jonathan-iap/CoilWinder/img/2016-08-17 12.49.52.jpg

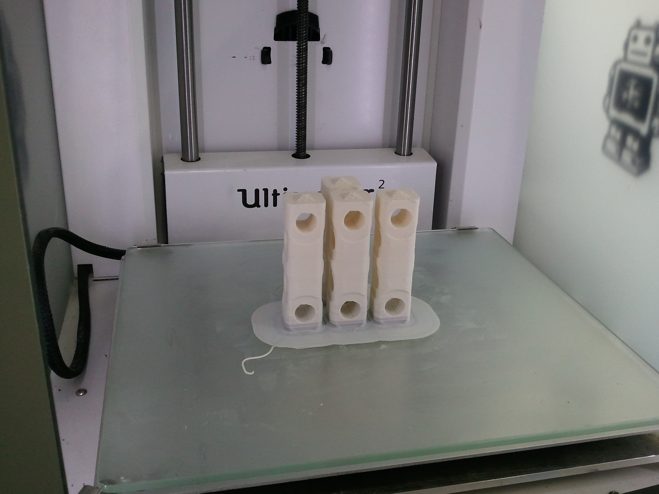
img/2016-08-17 12.49.52.jpg
