jonathan-iap/CoilWinder/img/2016-08-17 14.06.52.jpg

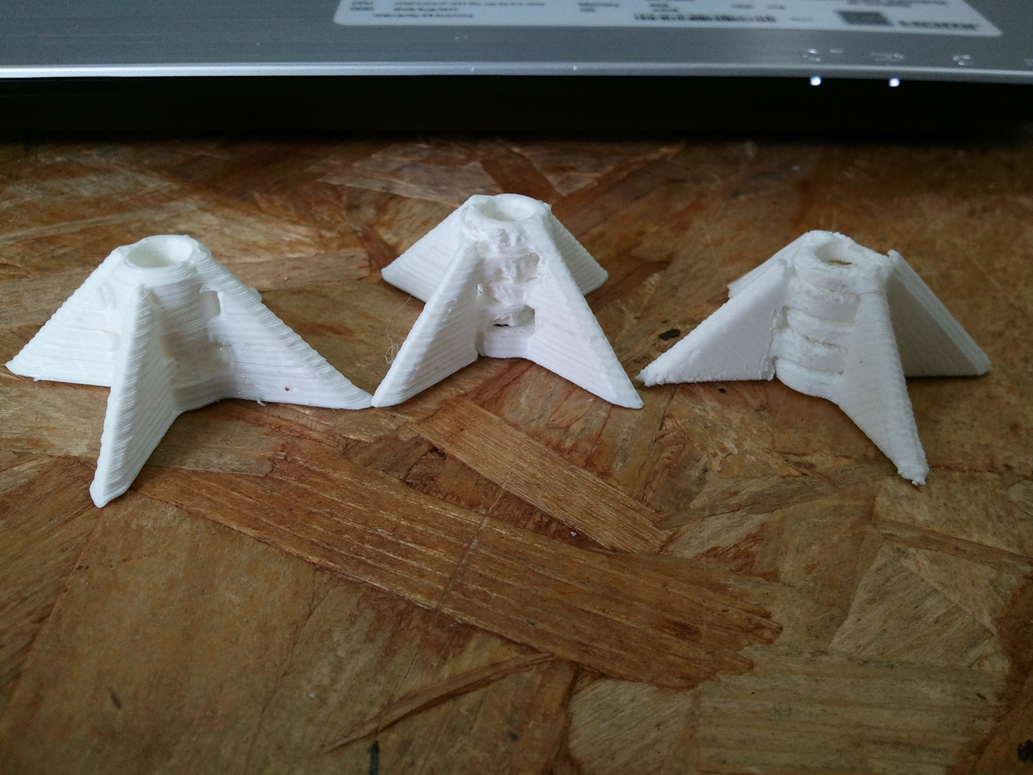
img/2016-08-17 14.06.52.jpg
