jonathan-iap/CoilWinder/img/2016-08-17 15.03.24.jpg

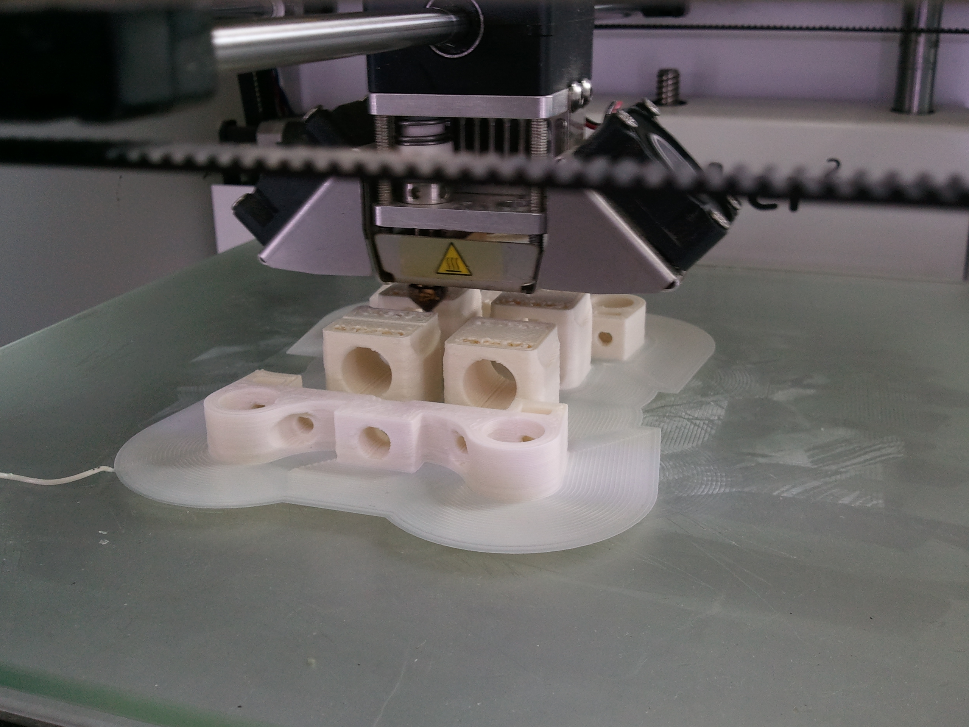
img/2016-08-17 15.03.24.jpg
