jonathan-iap/CoilWinder/img/2016-08-17 15.03.32.jpg

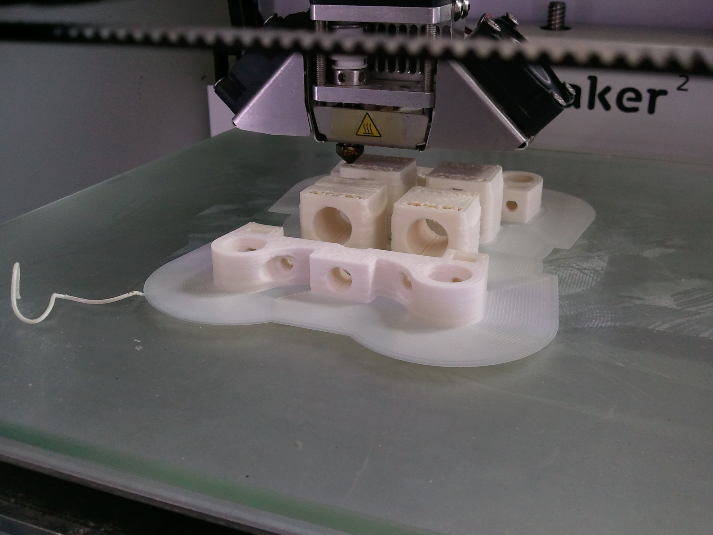
img/2016-08-17 15.03.32.jpg
