jonathan-iap/CoilWinder/img/2016-08-17 15.18.49.jpg

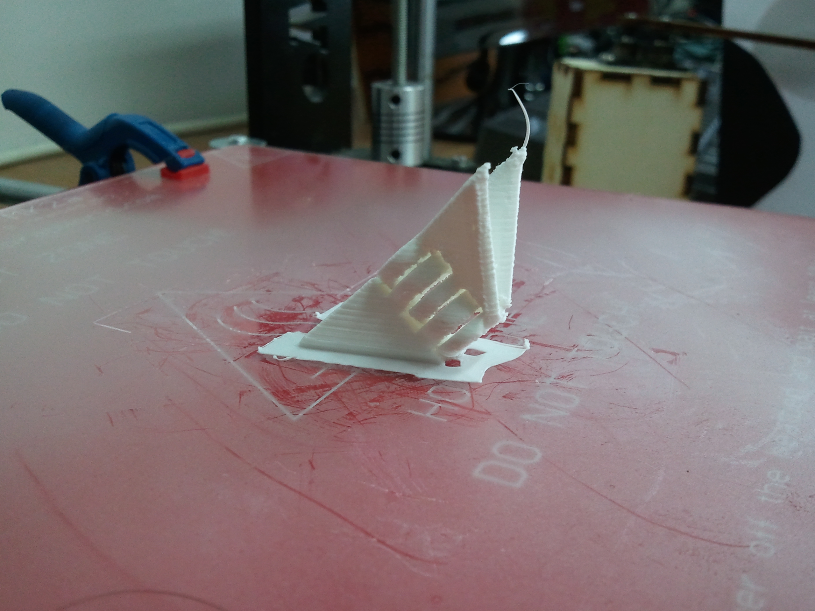
img/2016-08-17 15.18.49.jpg
