jonathan-iap/CoilWinder/img/2016-08-17 17.17.26.jpg

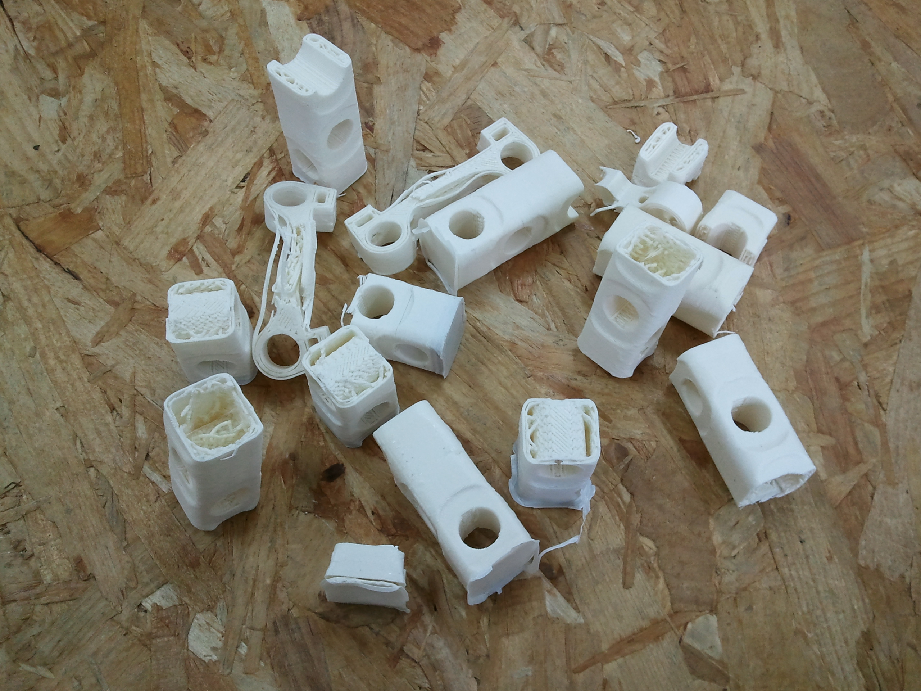
img/2016-08-17 17.17.26.jpg
