jonathan-iap/CoilWinder/img/2016-08-18 11.39.42.jpg

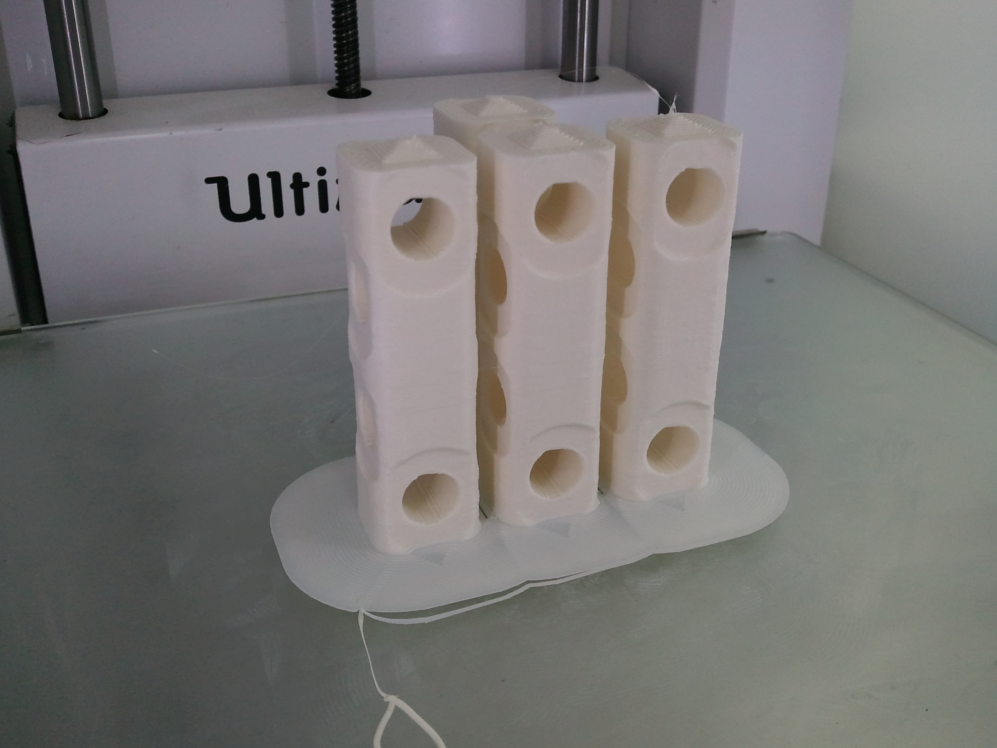
img/2016-08-18 11.39.42.jpg
