jonathan-iap/CoilWinder/img/2016-08-18 16.04.44.jpg

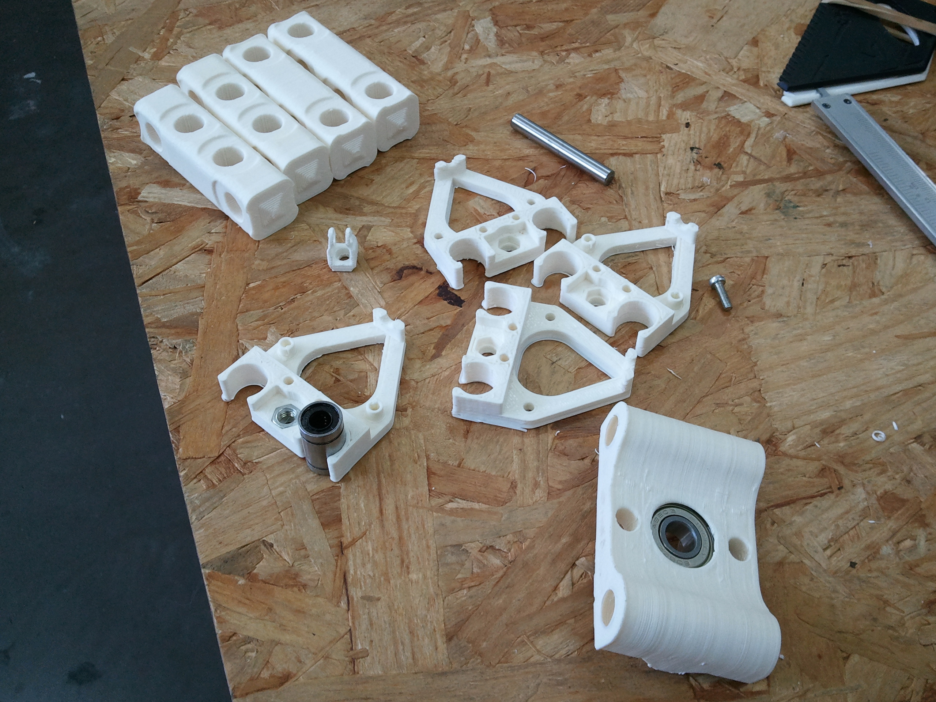
img/2016-08-18 16.04.44.jpg
