jonathan-iap/CoilWinder/img/2016-08-19 11.20.56.jpg

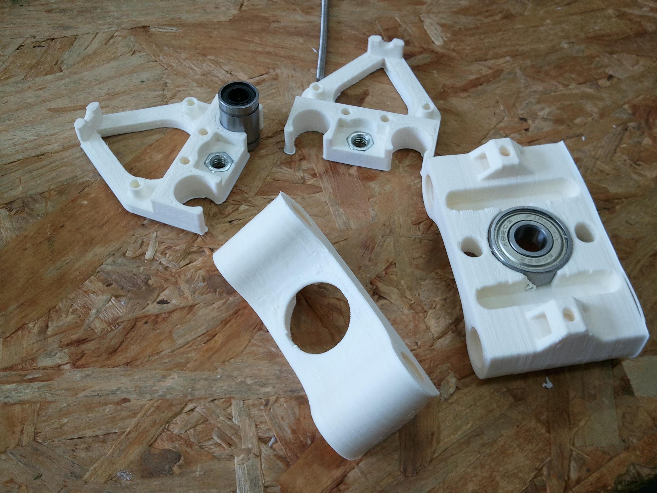
img/2016-08-19 11.20.56.jpg
