jonathan-iap/CoilWinder/img/2016-09-03 12.59.46.jpg

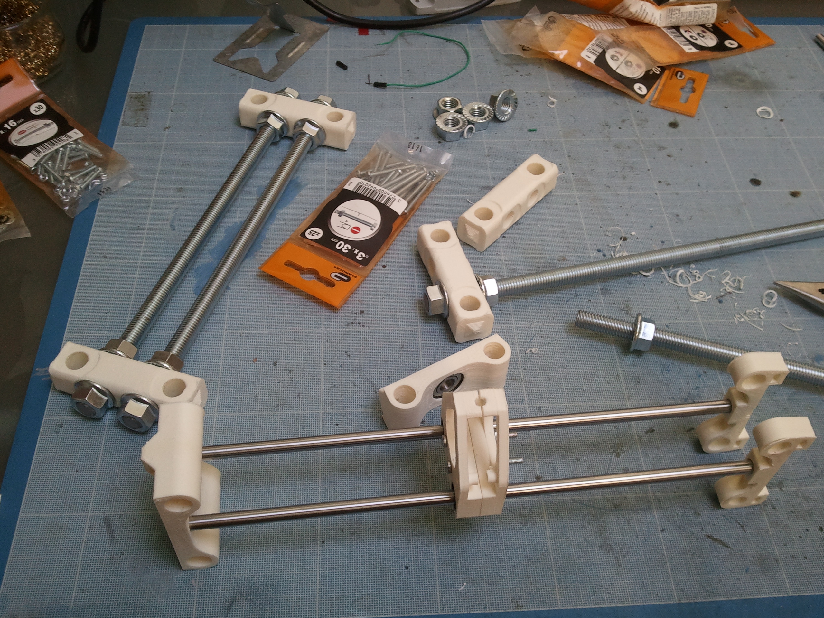
img/2016-09-03 12.59.46.jpg
