jonathan-iap/CoilWinder/img/2016-09-10 18.06.44.jpg

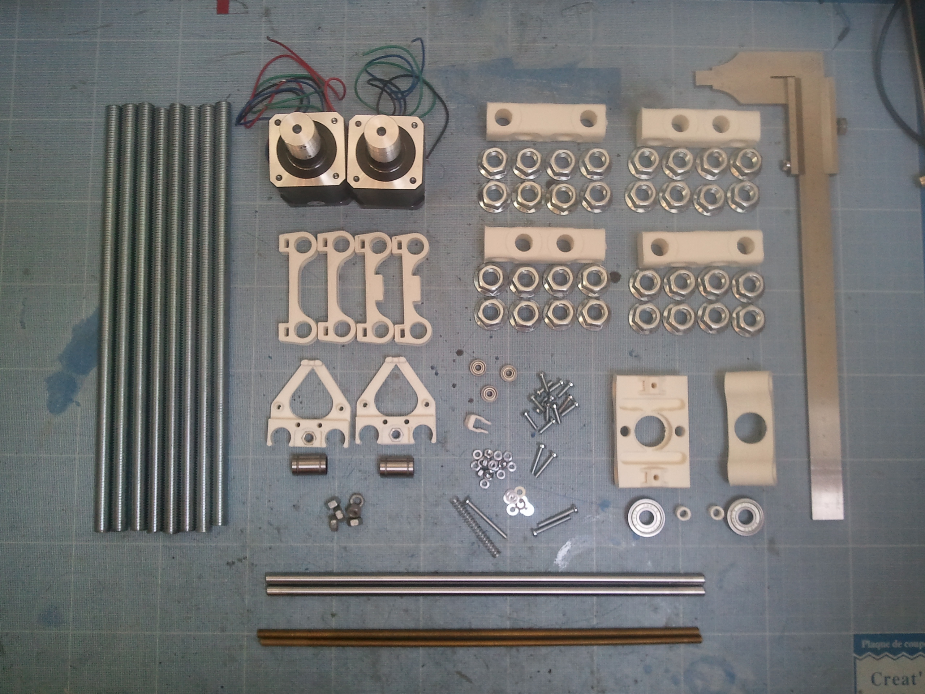
img/2016-09-10 18.06.44.jpg
