jonathan-iap/CoilWinder/img/2016-09-10 18.12.28.jpg

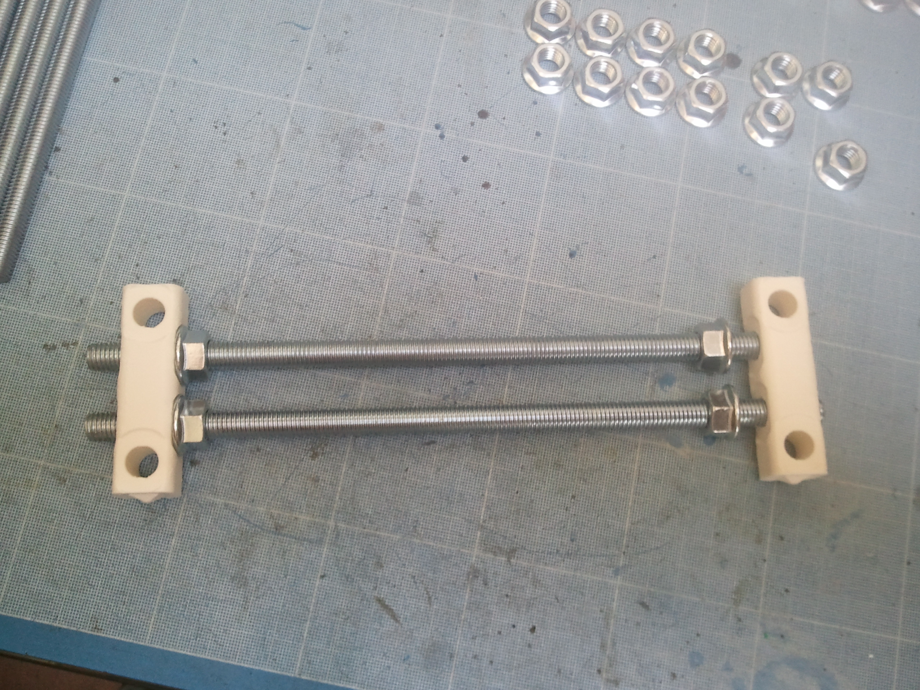
img/2016-09-10 18.12.28.jpg
