jonathan-iap/CoilWinder/img/2016-09-10 18.24.47.jpg

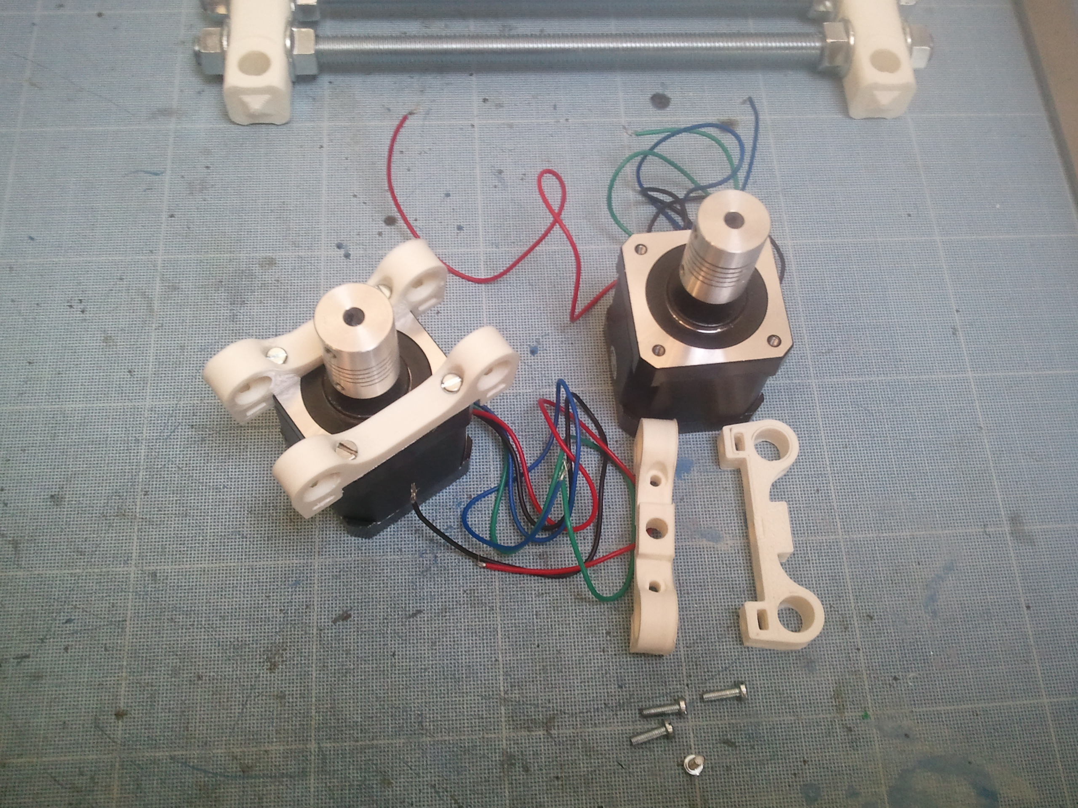
img/2016-09-10 18.24.47.jpg
