jonathan-iap/CoilWinder/img/2016-09-10 19.26.21.jpg

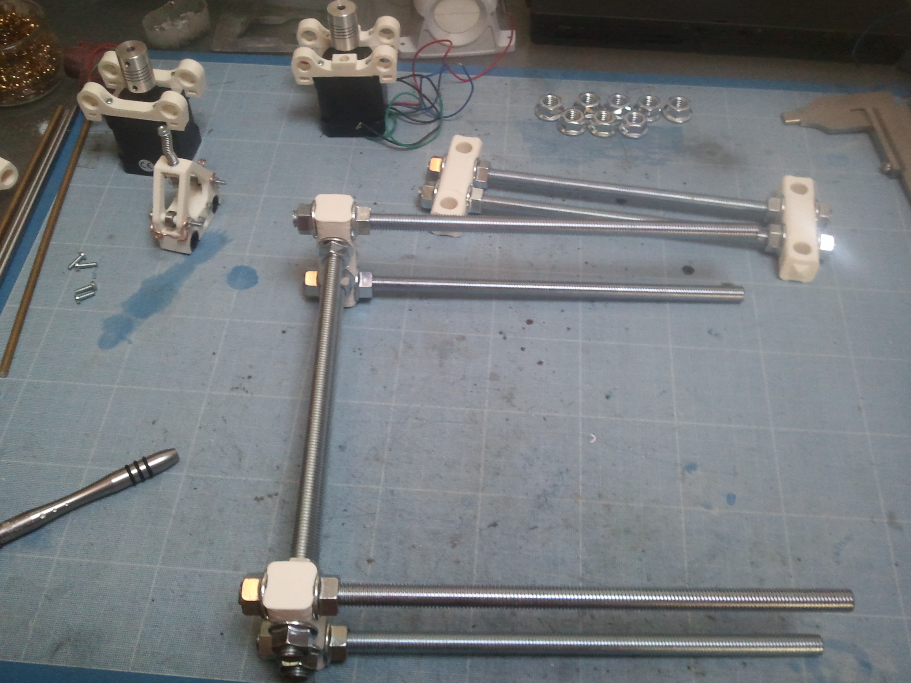
img/2016-09-10 19.26.21.jpg
