jonathan-iap/CoilWinder/img/2016-09-10 19.38.29.jpg

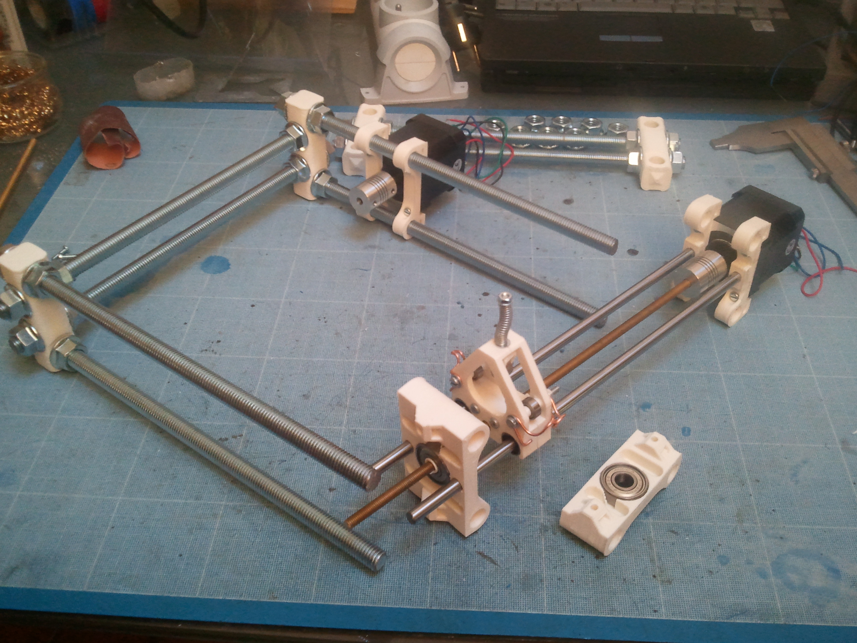
img/2016-09-10 19.38.29.jpg
