jonathan-iap/CoilWinder/img/2016-09-10 20.13.05.jpg

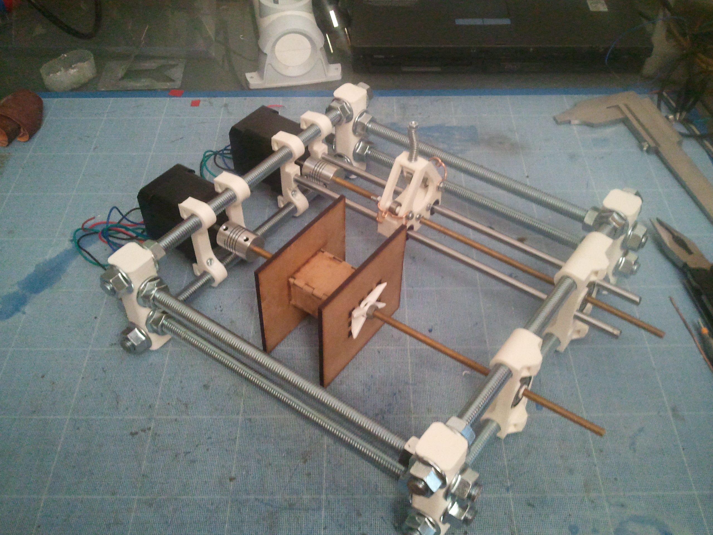
img/2016-09-10 20.13.05.jpg
