jonathan-iap/CoilWinder/img/2016-10-08 19.07.40.jpg

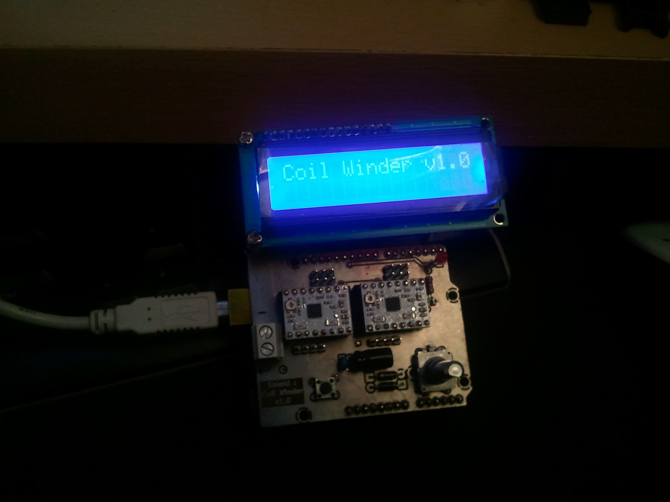
img/2016-10-08 19.07.40.jpg
