jonathan-iap/CoilWinder/img/2016-10-08 19.10.43.jpg

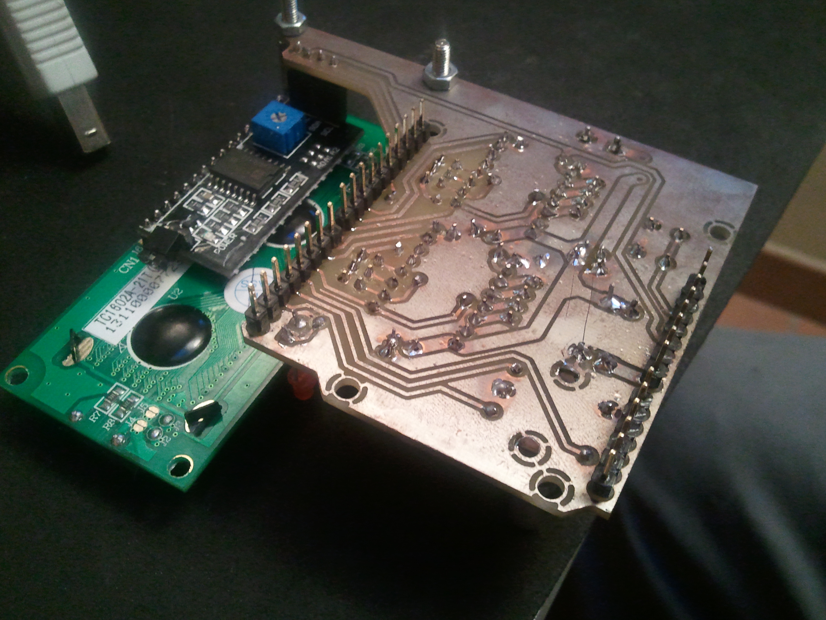
img/2016-10-08 19.10.43.jpg
