jonathan-iap/CoilWinder/img/2016-10-08 19.12.30.jpg

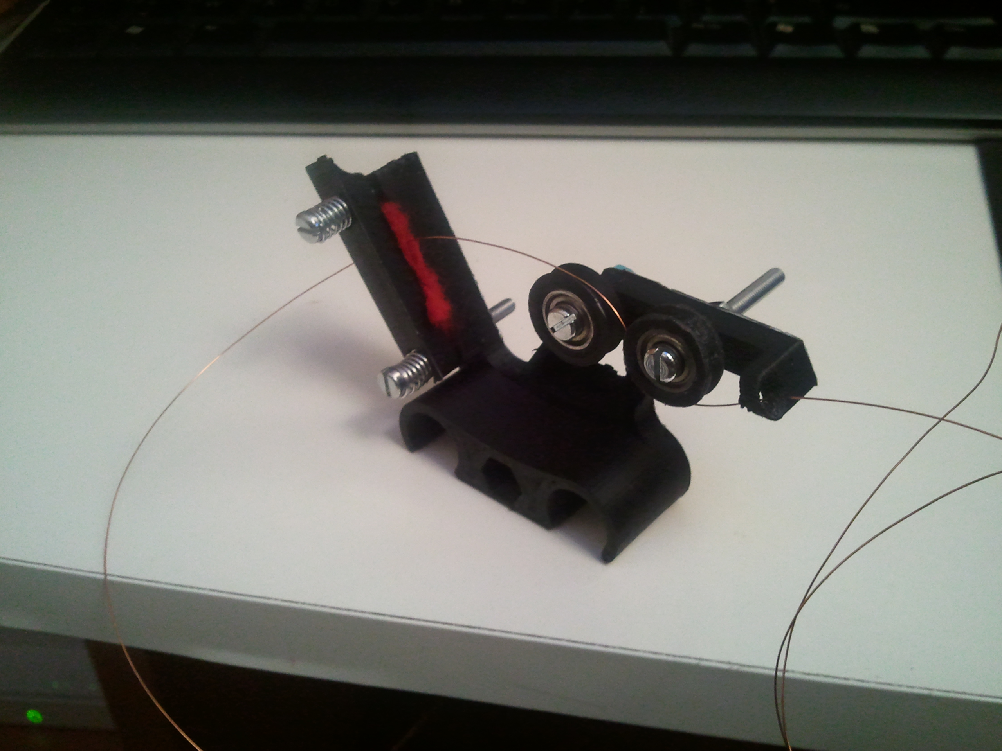
img/2016-10-08 19.12.30.jpg
