jonathan-iap/CoilWinder/STL_export/coin.stl

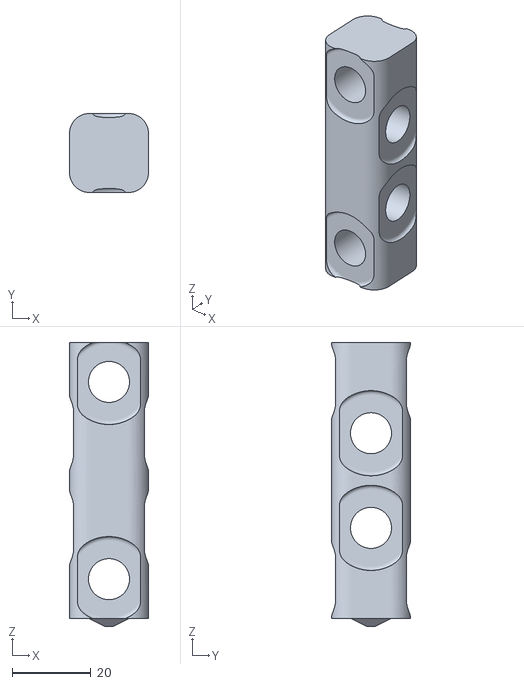
[picture p47: CAD file, 2017-12-31]
STL_export/coin.stl
20.0 x 20.0 x 72.0
