jonathan-iap/CoilWinder/STL_export/support axe guide fil_v0.2.stl

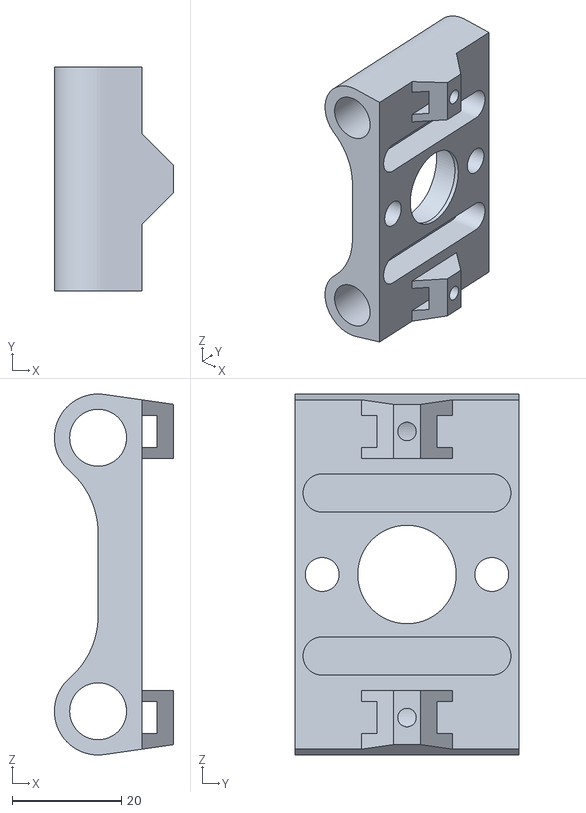
[picture p48: CAD file, 2017-12-29]
STL_export/support axe guide fil_v0.2.stl
21.8 x 41.0 x 66.0
