jonathan-iap/CoilWinder/Arduino/src/Motor.h

#ifndef MOTOR_H
#define MOTOR_H

#include "Arduino.h"
#include "Configuration.h"
#include "Fastio.h"
#include "TimerOne.h"

#define COIL      1
#define CARRIAGE  2

#define ACC 1000

#define MOTOR_INT 10 // motor interrupt in microseconds
#define RPM_TO_INT(rpm) ((600000 / rpm) / STEPS_PER_TR * MOTOR_INT)

#define WINDING   1
#define TRAVELING 2
#define ROTATION  3

void M_init();
void M_start();
void M_stop();
void M_engine();

void oneStep(bool M_coil, bool M_carr);
void updateCounter();

uint16_t M_getCoilTr();
bool M_getWindingStatus();
float M_getDisplacement();

void M_setMotors(bool M_coil, bool M_coilDir, bool M_carr, bool M_carrDir, uint16_t speed);
uint16_t M_setSpeed(uint16_t speed);
void M_invertSense();
void M_setSimpleDisplacement(uint8_t action, uint16_t pass, uint16_t steps);
void M_setWindingDisplacement(uint16_t pass, uint16_t steps, uint16_t tr,
			      uint16_t stepsTr, bool fastest);
void M_setWindingCounter(bool isNewCoil, bool isSuperior, uint16_t interval, uint16_t rest, uint16_t add);
void M_setState(bool isResume, uint16_t carrPass, uint16_t carrSteps, uint16_t coilTr, uint16_t coilSteps);
void M_getState(uint16_t *p_carrPass, uint16_t *p_carrSteps, bool *p_carrDir,
		uint16_t *p_coilTr, uint16_t *p_coilSteps, bool *p_coilDir);


#endif
