jonathan-iap/CoilWinder/Arduino/src/Fastio.h

/**
 * From Marlin 3D Printer Firmware
 * Copyright (C) 2016 MarlinFirmware [https://github.com/MarlinFirmware/Marlin]
 *
 * Based on Sprinter and grbl.
 * Copyright (C) 2011 Camiel Gubbels / Erik van der Zalm
 *
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
 */

/**
  This code contributed by Triffid_Hunter and modified by Kliment
  why double up on these macros? see http://gcc.gnu.org/onlinedocs/cpp/Stringification.html
 */

#ifndef _FASTIO_ARDUINO_H
#define _FASTIO_ARDUINO_H

#include <avr/io.h>

/**
  utility functions
 */

#ifndef MASK
#define MASK(PIN)  (1 << PIN)
#endif

// Bracket code that shouldn't be interrupted
#ifndef CRITICAL_SECTION_START
#define CRITICAL_SECTION_START  unsigned char _sreg = SREG; cli();
#define CRITICAL_SECTION_END    SREG = _sreg;
#endif

/**
  magic I/O routines
  now you can simply SET_OUTPUT(STEP); WRITE(STEP, 1); WRITE(STEP, 0);
 */

/// Read a pin
#define _READ(IO) ((bool)(DIO ## IO ## _RPORT & MASK(DIO ## IO ## _PIN)))
/// write to a pin
// On some boards pins > 0x100 are used. These are not converted to atomic actions. An critical section is needed.

#define _WRITE_NC(IO, v)  do { if (v) {DIO ##  IO ## _WPORT |= MASK(DIO ## IO ## _PIN); } else {DIO ##  IO ## _WPORT &= ~MASK(DIO ## IO ## _PIN); }; } while (0)

#define _WRITE_C(IO, v)   do { if (v) { \
    CRITICAL_SECTION_START; \
    {DIO ##  IO ## _WPORT |= MASK(DIO ## IO ## _PIN); } \
    CRITICAL_SECTION_END; \
} \
else { \
    CRITICAL_SECTION_START; \
    {DIO ##  IO ## _WPORT &= ~MASK(DIO ## IO ## _PIN); } \
    CRITICAL_SECTION_END; \
} \
} \
while (0)

#define _WRITE(IO, v)  do {  if (&(DIO ##  IO ## _RPORT) >= (uint8_t *)0x100) {_WRITE_C(IO, v); } else {_WRITE_NC(IO, v); }; } while (0)

/// toggle a pin
#define _TOGGLE(IO)  do {DIO ##  IO ## _RPORT = MASK(DIO ## IO ## _PIN); } while (0)

/// set pin as input
#define _SET_INPUT(IO) do {DIO ##  IO ## _DDR &= ~MASK(DIO ## IO ## _PIN); } while (0)
/// set pin as output
#define _SET_OUTPUT(IO) do {DIO ##  IO ## _DDR |=  MASK(DIO ## IO ## _PIN); } while (0)

/// check if pin is an input
#define _GET_INPUT(IO)  ((DIO ## IO ## _DDR & MASK(DIO ## IO ## _PIN)) == 0)
/// check if pin is an output
#define _GET_OUTPUT(IO)  ((DIO ## IO ## _DDR & MASK(DIO ## IO ## _PIN)) != 0)

/// check if pin is an timer
#define _GET_TIMER(IO)  ((DIO ## IO ## _PWM)

//  why double up on these macros? see http://gcc.gnu.org/onlinedocs/cpp/Stringification.html

/// Read a pin wrapper
#define READ(IO)  _READ(IO)
/// Write to a pin wrapper
#define WRITE(IO, v)  _WRITE(IO, v)

/// toggle a pin wrapper
#define TOGGLE(IO)  _TOGGLE(IO)

/// set pin as input wrapper
#define SET_INPUT(IO)  _SET_INPUT(IO)
/// set pin as output wrapper
#define SET_OUTPUT(IO)  _SET_OUTPUT(IO)

/// check if pin is an input wrapper
#define GET_INPUT(IO)  _GET_INPUT(IO)
/// check if pin is an output wrapper
#define GET_OUTPUT(IO)  _GET_OUTPUT(IO)

/// check if pin is an timer wrapper
#define GET_TIMER(IO)  _GET_TIMER(IO)

// Shorthand
#define OUT_WRITE(IO, v) { SET_OUTPUT(IO); WRITE(IO, v); }

/**
  ports and functions

  added as necessary or if I feel like it- not a comprehensive list!
 */

#if defined(__AVR_ATmega168__) || defined(__AVR_ATmega328__) || defined(__AVR_ATmega328P__)
// UART
#define RXD         DIO0
#define TXD         DIO1

// SPI
#define SCK         DIO13
#define MISO        DIO12
#define MOSI        DIO11
#define SS          DIO10

// TWI (I2C)
#define SCL         AIO5
#define SDA         AIO4

// timers and PWM
#define OC0A        DIO6
#define OC0B        DIO5
#define OC1A        DIO9
#define OC1B        DIO10
#define OC2A        DIO11
#define OC2B        DIO3

#define DEBUG_LED   AIO5

/**
  pins
 */

#define DIO0_PIN    PIND0
#define DIO0_RPORT  PIND
#define DIO0_WPORT  PORTD
#define DIO0_DDR    DDRD
#define DIO0_PWM    NULL

#define DIO1_PIN    PIND1
#define DIO1_RPORT  PIND
#define DIO1_WPORT  PORTD
#define DIO1_DDR    DDRD
#define DIO1_PWM    NULL

#define DIO2_PIN    PIND2
#define DIO2_RPORT  PIND
#define DIO2_WPORT  PORTD
#define DIO2_DDR    DDRD
#define DIO2_PWM    NULL

#define DIO3_PIN    PIND3
#define DIO3_RPORT  PIND
#define DIO3_WPORT  PORTD
#define DIO3_DDR    DDRD
#define DIO3_PWM    &OCR2B

#define DIO4_PIN    PIND4
#define DIO4_RPORT  PIND
#define DIO4_WPORT  PORTD
#define DIO4_DDR    DDRD
#define DIO4_PWM    NULL

#define DIO5_PIN    PIND5
#define DIO5_RPORT  PIND
#define DIO5_WPORT  PORTD
#define DIO5_DDR    DDRD
#define DIO5_PWM    &OCR0B

#define DIO6_PIN    PIND6
#define DIO6_RPORT  PIND
#define DIO6_WPORT  PORTD
#define DIO6_DDR    DDRD
#define DIO6_PWM    &OCR0A

#define DIO7_PIN    PIND7
#define DIO7_RPORT  PIND
#define DIO7_WPORT  PORTD
#define DIO7_DDR    DDRD
#define DIO7_PWM    NULL

#define DIO8_PIN    PINB0
#define DIO8_RPORT  PINB
#define DIO8_WPORT  PORTB
#define DIO8_DDR    DDRB
#define DIO8_PWM    NULL

#define DIO9_PIN    PINB1
#define DIO9_RPORT  PINB
#define DIO9_WPORT  PORTB
#define DIO9_DDR    DDRB
#define DIO9_PWM    NULL

#define DIO10_PIN   PINB2
#define DIO10_RPORT PINB
#define DIO10_WPORT PORTB
#define DIO10_DDR   DDRB
#define DIO10_PWM   NULL

#define DIO11_PIN   PINB3
#define DIO11_RPORT PINB
#define DIO11_WPORT PORTB
#define DIO11_DDR   DDRB
#define DIO11_PWM   &OCR2A

#define DIO12_PIN   PINB4
#define DIO12_RPORT PINB
#define DIO12_WPORT PORTB
#define DIO12_DDR   DDRB
#define DIO12_PWM   NULL

#define DIO13_PIN   PINB5
#define DIO13_RPORT PINB
#define DIO13_WPORT PORTB
#define DIO13_DDR   DDRB
#define DIO13_PWM   NULL


#define DIO14_PIN   PINC0
#define DIO14_RPORT PINC
#define DIO14_WPORT PORTC
#define DIO14_DDR   DDRC
#define DIO14_PWM   NULL

#define DIO15_PIN   PINC1
#define DIO15_RPORT PINC
#define DIO15_WPORT PORTC
#define DIO15_DDR   DDRC
#define DIO15_PWM   NULL

#define DIO16_PIN   PINC2
#define DIO16_RPORT PINC
#define DIO16_WPORT PORTC
#define DIO16_DDR   DDRC
#define DIO16_PWM   NULL

#define DIO17_PIN   PINC3
#define DIO17_RPORT PINC
#define DIO17_WPORT PORTC
#define DIO17_DDR   DDRC
#define DIO17_PWM   NULL

#define DIO18_PIN   PINC4
#define DIO18_RPORT PINC
#define DIO18_WPORT PORTC
#define DIO18_DDR   DDRC
#define DIO18_PWM   NULL

#define DIO19_PIN   PINC5
#define DIO19_RPORT PINC
#define DIO19_WPORT PORTC
#define DIO19_DDR   DDRC
#define DIO19_PWM   NULL

#define DIO20_PIN   PINC6
#define DIO20_RPORT PINC
#define DIO20_WPORT PORTC
#define DIO20_DDR   DDRC
#define DIO20_PWM   NULL

#define DIO21_PIN   PINC7
#define DIO21_RPORT PINC
#define DIO21_WPORT PORTC
#define DIO21_DDR   DDRC
#define DIO21_PWM   NULL



#undef PB0
#define PB0_PIN     PINB0
#define PB0_RPORT   PINB
#define PB0_WPORT   PORTB
#define PB0_DDR     DDRB
#define PB0_PWM     NULL

#undef PB1
#define PB1_PIN     PINB1
#define PB1_RPORT   PINB
#define PB1_WPORT   PORTB
#define PB1_DDR     DDRB
#define PB1_PWM     NULL

#undef PB2
#define PB2_PIN     PINB2
#define PB2_RPORT   PINB
#define PB2_WPORT   PORTB
#define PB2_DDR     DDRB
#define PB2_PWM     NULL

#undef PB3
#define PB3_PIN     PINB3
#define PB3_RPORT   PINB
#define PB3_WPORT   PORTB
#define PB3_DDR     DDRB
#define PB3_PWM     &OCR2A

#undef PB4
#define PB4_PIN     PINB4
#define PB4_RPORT   PINB
#define PB4_WPORT   PORTB
#define PB4_DDR     DDRB
#define PB4_PWM     NULL

#undef PB5
#define PB5_PIN     PINB5
#define PB5_RPORT   PINB
#define PB5_WPORT   PORTB
#define PB5_DDR     DDRB
#define PB5_PWM     NULL

#undef PB6
#define PB6_PIN     PINB6
#define PB6_RPORT   PINB
#define PB6_WPORT   PORTB
#define PB6_DDR     DDRB
#define PB6_PWM     NULL

#undef PB7
#define PB7_PIN     PINB7
#define PB7_RPORT   PINB
#define PB7_WPORT   PORTB
#define PB7_DDR     DDRB
#define PB7_PWM     NULL


#undef PC0
#define PC0_PIN     PINC0
#define PC0_RPORT   PINC
#define PC0_WPORT   PORTC
#define PC0_DDR     DDRC
#define PC0_PWM     NULL

#undef PC1
#define PC1_PIN     PINC1
#define PC1_RPORT   PINC
#define PC1_WPORT   PORTC
#define PC1_DDR     DDRC
#define PC1_PWM     NULL

#undef PC2
#define PC2_PIN     PINC2
#define PC2_RPORT   PINC
#define PC2_WPORT   PORTC
#define PC2_DDR     DDRC
#define PC2_PWM     NULL

#undef PC3
#define PC3_PIN     PINC3
#define PC3_RPORT   PINC
#define PC3_WPORT   PORTC
#define PC3_DDR     DDRC
#define PC3_PWM     NULL

#undef PC4
#define PC4_PIN     PINC4
#define PC4_RPORT   PINC
#define PC4_WPORT   PORTC
#define PC4_DDR     DDRC
#define PC4_PWM     NULL

#undef PC5
#define PC5_PIN     PINC5
#define PC5_RPORT   PINC
#define PC5_WPORT   PORTC
#define PC5_DDR     DDRC
#define PC5_PWM     NULL

#undef PC6
#define PC6_PIN     PINC6
#define PC6_RPORT   PINC
#define PC6_WPORT   PORTC
#define PC6_DDR     DDRC
#define PC6_PWM     NULL

#undef PC7
#define PC7_PIN     PINC7
#define PC7_RPORT   PINC
#define PC7_WPORT   PORTC
#define PC7_DDR     DDRC
#define PC7_PWM     NULL


#undef PD0
#define PD0_PIN     PIND0
#define PD0_RPORT   PIND
#define PD0_WPORT   PORTD
#define PD0_DDR     DDRD
#define PD0_PWM     NULL

#undef PD1
#define PD1_PIN     PIND1
#define PD1_RPORT   PIND
#define PD1_WPORT   PORTD
#define PD1_DDR     DDRD
#define PD1_PWM     NULL

#undef PD2
#define PD2_PIN     PIND2
#define PD2_RPORT   PIND
#define PD2_WPORT   PORTD
#define PD2_DDR     DDRD
#define PD2_PWM     NULL

#undef PD3
#define PD3_PIN     PIND3
#define PD3_RPORT   PIND
#define PD3_WPORT   PORTD
#define PD3_DDR     DDRD
#define PD3_PWM     &OCR2B

#undef PD4
#define PD4_PIN     PIND4
#define PD4_RPORT   PIND
#define PD4_WPORT   PORTD
#define PD4_DDR     DDRD
#define PD4_PWM     NULL

#undef PD5
#define PD5_PIN     PIND5
#define PD5_RPORT   PIND
#define PD5_WPORT   PORTD
#define PD5_DDR     DDRD
#define PD5_PWM     &OCR0B

#undef PD6
#define PD6_PIN     PIND6
#define PD6_RPORT   PIND
#define PD6_WPORT   PORTD
#define PD6_DDR     DDRD
#define PD6_PWM     &OCR0A

#undef PD7
#define PD7_PIN     PIND7
#define PD7_RPORT   PIND
#define PD7_WPORT   PORTD
#define PD7_DDR     DDRD
#define PD7_PWM     NULL
#endif  /*  _AVR_ATmega{168,328,328P}__ */

#if defined(__AVR_ATmega644__) || defined(__AVR_ATmega644P__) || defined(__AVR_ATmega644PA__) || defined(__AVR_ATmega1284P__)
// UART
#define RXD         DIO8
#define TXD         DIO9
#define RXD0        DIO8
#define TXD0        DIO9

#define RXD1        DIO10
#define TXD1        DIO11

// SPI
#define SCK         DIO7
#define MISO        DIO6
#define MOSI        DIO5
#define SS          DIO4

// TWI (I2C)
#define SCL         DIO16
#define SDA         DIO17

// timers and PWM
#define OC0A        DIO3
#define OC0B        DIO4
#define OC1A        DIO13
#define OC1B        DIO12
#define OC2A        DIO15
#define OC2B        DIO14

#define DEBUG_LED   DIO0
/**
  pins
 */

#define DIO0_PIN    PINB0
#define DIO0_RPORT  PINB
#define DIO0_WPORT  PORTB
#define DIO0_DDR    DDRB
#define DIO0_PWM    NULL

#define DIO1_PIN    PINB1
#define DIO1_RPORT  PINB
#define DIO1_WPORT  PORTB
#define DIO1_DDR    DDRB
#define DIO1_PWM    NULL

#define DIO2_PIN    PINB2
#define DIO2_RPORT  PINB
#define DIO2_WPORT  PORTB
#define DIO2_DDR    DDRB
#define DIO2_PWM    NULL

#define DIO3_PIN    PINB3
#define DIO3_RPORT  PINB
#define DIO3_WPORT  PORTB
#define DIO3_DDR    DDRB
#define DIO3_PWM    OCR0A

#define DIO4_PIN    PINB4
#define DIO4_RPORT  PINB
#define DIO4_WPORT  PORTB
#define DIO4_DDR    DDRB
#define DIO4_PWM    OCR0B

#define DIO5_PIN    PINB5
#define DIO5_RPORT  PINB
#define DIO5_WPORT  PORTB
#define DIO5_DDR    DDRB
#define DIO5_PWM    NULL

#define DIO6_PIN    PINB6
#define DIO6_RPORT  PINB
#define DIO6_WPORT  PORTB
#define DIO6_DDR    DDRB
#define DIO6_PWM    NULL

#define DIO7_PIN    PINB7
#define DIO7_RPORT  PINB
#define DIO7_WPORT  PORTB
#define DIO7_DDR    DDRB
#define DIO7_PWM    NULL

#define DIO8_PIN    PIND0
#define DIO8_RPORT  PIND
#define DIO8_WPORT  PORTD
#define DIO8_DDR    DDRD
#define DIO8_PWM    NULL

#define DIO9_PIN    PIND1
#define DIO9_RPORT  PIND
#define DIO9_WPORT  PORTD
#define DIO9_DDR    DDRD
#define DIO9_PWM    NULL

#define DIO10_PIN   PIND2
#define DIO10_RPORT PIND
#define DIO10_WPORT PORTD
#define DIO10_DDR   DDRD
#define DIO10_PWM   NULL

#define DIO11_PIN   PIND3
#define DIO11_RPORT PIND
#define DIO11_WPORT PORTD
#define DIO11_DDR   DDRD
#define DIO11_PWM   NULL

#define DIO12_PIN   PIND4
#define DIO12_RPORT PIND
#define DIO12_WPORT PORTD
#define DIO12_DDR   DDRD
#define DIO12_PWM   OCR1B

#define DIO13_PIN   PIND5
#define DIO13_RPORT PIND
#define DIO13_WPORT PORTD
#define DIO13_DDR   DDRD
#define DIO13_PWM   OCR1A

#define DIO14_PIN   PIND6
#define DIO14_RPORT PIND
#define DIO14_WPORT PORTD
#define DIO14_DDR   DDRD
#define DIO14_PWM   OCR2B

#define DIO15_PIN   PIND7
#define DIO15_RPORT PIND
#define DIO15_WPORT PORTD
#define DIO15_DDR   DDRD
#define DIO15_PWM   OCR2A

#define DIO16_PIN   PINC0
#define DIO16_RPORT PINC
#define DIO16_WPORT PORTC
#define DIO16_DDR   DDRC
#define DIO16_PWM   NULL

#define DIO17_PIN   PINC1
#define DIO17_RPORT PINC
#define DIO17_WPORT PORTC
#define DIO17_DDR   DDRC
#define DIO17_PWM   NULL

#define DIO18_PIN   PINC2
#define DIO18_RPORT PINC
#define DIO18_WPORT PORTC
#define DIO18_DDR   DDRC
#define DIO18_PWM   NULL

#define DIO19_PIN   PINC3
#define DIO19_RPORT PINC
#define DIO19_WPORT PORTC
#define DIO19_DDR   DDRC
#define DIO19_PWM   NULL

#define DIO20_PIN   PINC4
#define DIO20_RPORT PINC
#define DIO20_WPORT PORTC
#define DIO20_DDR   DDRC
#define DIO20_PWM   NULL

#define DIO21_PIN   PINC5
#define DIO21_RPORT PINC
#define DIO21_WPORT PORTC
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
// UART
#define RXD         DIO0
#define TXD         DIO1

// SPI
#define SCK         DIO52
#define MISO        DIO50
#define MOSI        DIO51
#define SS          DIO53

// TWI (I2C)
#define SCL         DIO21
#define SDA         DIO20

// timers and PWM
#define OC0A        DIO13
#define OC0B        DIO4
#define OC1A        DIO11
#define OC1B        DIO12
#define OC2A        DIO10
#define OC2B        DIO9
#define OC3A        DIO5
#define OC3B        DIO2
#define OC3C        DIO3
#define OC4A        DIO6
#define OC4B        DIO7
#define OC4C        DIO8
#define OC5A        DIO46
#define OC5B        DIO45
#define OC5C        DIO44

// change for your board
#define DEBUG_LED   DIO21

/**
  pins
 */
#define DIO0_PIN    PINE0
#define DIO0_RPORT  PINE
#define DIO0_WPORT  PORTE
#define DIO0_DDR    DDRE
#define DIO0_PWM    NULL

#define DIO1_PIN    PINE1
#define DIO1_RPORT  PINE
#define DIO1_WPORT  PORTE
#define DIO1_DDR    DDRE
#define DIO1_PWM    NULL

#define DIO2_PIN    PINE4
#define DIO2_RPORT  PINE
#define DIO2_WPORT  PORTE
#define DIO2_DDR    DDRE
#define DIO2_PWM    &OCR3BL

#define DIO3_PIN    PINE5
#define DIO3_RPORT  PINE
#define DIO3_WPORT  PORTE
#define DIO3_DDR    DDRE
#define DIO3_PWM    &OCR3CL

#define DIO4_PIN    PING5
#define DIO4_RPORT  PING
#define DIO4_WPORT  PORTG
#define DIO4_DDR    DDRG
#define DIO4_PWM    &OCR0B

#define DIO5_PIN    PINE3
#define DIO5_RPORT  PINE
#define DIO5_WPORT  PORTE
#define DIO5_DDR    DDRE
#define DIO5_PWM    &OCR3AL

#define DIO6_PIN    PINH3
#define DIO6_RPORT  PINH
#define DIO6_WPORT  PORTH
#define DIO6_DDR    DDRH
#define DIO6_PWM    &OCR4AL

#define DIO7_PIN    PINH4
#define DIO7_RPORT  PINH
#define DIO7_WPORT  PORTH
#define DIO7_DDR    DDRH
#define DIO7_PWM    &OCR4BL

#define DIO8_PIN    PINH5
#define DIO8_RPORT  PINH
#define DIO8_WPORT  PORTH
#define DIO8_DDR    DDRH
#define DIO8_PWM    &OCR4CL

#define DIO9_PIN    PINH6
#define DIO9_RPORT  PINH
#define DIO9_WPORT  PORTH
#define DIO9_DDR    DDRH
#define DIO9_PWM    &OCR2B

#define DIO10_PIN   PINB4
#define DIO10_RPORT PINB
#define DIO10_WPORT PORTB
#define DIO10_DDR   DDRB
#define DIO10_PWM   &OCR2A

#define DIO11_PIN   PINB5
#define DIO11_RPORT PINB
#define DIO11_WPORT PORTB
#define DIO11_DDR   DDRB
#define DIO11_PWM   NULL

#define DIO12_PIN   PINB6
#define DIO12_RPORT PINB
#define DIO12_WPORT PORTB
#define DIO12_DDR   DDRB
#define DIO12_PWM   NULL

#define DIO13_PIN   PINB7
#define DIO13_RPORT PINB
#define DIO13_WPORT PORTB
#define DIO13_DDR   DDRB
#define DIO13_PWM   &OCR0A

#define DIO14_PIN   PINJ1
#define DIO14_RPORT PINJ
#define DIO14_WPORT PORTJ
#define DIO14_DDR   DDRJ
#define DIO14_PWM   NULL

#define DIO15_PIN   PINJ0
#define DIO15_RPORT PINJ
#define DIO15_WPORT PORTJ
#define DIO15_DDR   DDRJ
#define DIO15_PWM   NULL

#define DIO16_PIN   PINH1
#define DIO16_RPORT PINH
#define DIO16_WPORT PORTH
#define DIO16_DDR   DDRH
#define DIO16_PWM   NULL

#define DIO17_PIN   PINH0
#define DIO17_RPORT PINH
#define DIO17_WPORT PORTH
#define DIO17_DDR   DDRH
#define DIO17_PWM   NULL

#define DIO18_PIN   PIND3
#define DIO18_RPORT PIND
#define DIO18_WPORT PORTD
#define DIO18_DDR   DDRD
#define DIO18_PWM   NULL

#define DIO19_PIN   PIND2
#define DIO19_RPORT PIND
#define DIO19_WPORT PORTD
#define DIO19_DDR   DDRD
#define DIO19_PWM   NULL

#define DIO20_PIN   PIND1
#define DIO20_RPORT PIND
#define DIO20_WPORT PORTD
#define DIO20_DDR   DDRD
#define DIO20_PWM   NULL

#define DIO21_PIN   PIND0
#define DIO21_RPORT PIND
#define DIO21_WPORT PORTD
#define DIO21_DDR   DDRD
#define DIO21_PWM   NULL

#define DIO22_PIN   PINA0
#define DIO22_RPORT PINA
#define DIO22_WPORT PORTA
#define DIO22_DDR   DDRA
#define DIO22_PWM   NULL

#define DIO23_PIN   PINA1
#define DIO23_RPORT PINA
#define DIO23_WPORT PORTA
#define DIO23_DDR   DDRA
#define DIO23_PWM   NULL

#define DIO24_PIN   PINA2
#define DIO24_RPORT PINA
#define DIO24_WPORT PORTA
#define DIO24_DDR   DDRA
#define DIO24_PWM   NULL

#define DIO25_PIN   PINA3
#define DIO25_RPORT PINA
#define DIO25_WPORT PORTA
#define DIO25_DDR   DDRA
#define DIO25_PWM   NULL

#define DIO26_PIN   PINA4
#define DIO26_RPORT PINA
#define DIO26_WPORT PORTA
#define DIO26_DDR   DDRA
#define DIO26_PWM   NULL

#define DIO27_PIN   PINA5
#define DIO27_RPORT PINA
#define DIO27_WPORT PORTA
#define DIO27_DDR   DDRA
#define DIO27_PWM   NULL

#define DIO28_PIN   PINA6
#define DIO28_RPORT PINA
#define DIO28_WPORT PORTA
#define DIO28_DDR   DDRA
#define DIO28_PWM   NULL

#define DIO29_PIN   PINA7
#define DIO29_RPORT PINA
#define DIO29_WPORT PORTA
#define DIO29_DDR   DDRA
#define DIO29_PWM   NULL

#define DIO30_PIN   PINC7
#define DIO30_RPORT PINC
#define DIO30_WPORT PORTC
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
#define PE5_PWM NULL
#define PE5_DDR DDRE
#undef PE6
#define PE6_PIN PINE6
#define PE6_RPORT PINE
#define PE6_WPORT PORTE
#define PE6_PWM NULL
#define PE6_DDR DDRE
#undef PE7
#define PE7_PIN PINE7
#define PE7_RPORT PINE
#define PE7_WPORT PORTE
#define PE7_PWM NULL
#define PE7_DDR DDRE

#undef PF0
#define PF0_PIN PINF0
#define PF0_RPORT PINF
#define PF0_WPORT PORTF
#define PF0_PWM NULL
#define PF0_DDR DDRF
#undef PF1
#define PF1_PIN PINF1
#define PF1_RPORT PINF
#define PF1_WPORT PORTF
#define PF1_PWM NULL
#define PF1_DDR DDRF
#undef PF2
#define PF2_PIN PINF2
#define PF2_RPORT PINF
#define PF2_WPORT PORTF
#define PF2_PWM NULL
#define PF2_DDR DDRF
#undef PF3
#define PF3_PIN PINF3
#define PF3_RPORT PINF
#define PF3_WPORT PORTF
#define PF3_PWM NULL
#define PF3_DDR DDRF
#undef PF4
#define PF4_PIN PINF4
#define PF4_RPORT PINF
#define PF4_WPORT PORTF
#define PF4_PWM NULL
#define PF4_DDR DDRF
#undef PF5
#define PF5_PIN PINF5
#define PF5_RPORT PINF
#define PF5_WPORT PORTF
#define PF5_PWM NULL
#define PF5_DDR DDRF
#undef PF6
#define PF6_PIN PINF6
#define PF6_RPORT PINF
#define PF6_WPORT PORTF
#define PF6_PWM NULL
#define PF6_DDR DDRF
#undef PF7
#define PF7_PIN PINF7
#define PF7_RPORT PINF
#define PF7_WPORT PORTF
#define PF7_PWM NULL
#define PF7_DDR DDRF

#endif // AT90USBxx_TEENSYPP_ASSIGNMENTS Teensyduino assignments
#endif // __AVR_AT90usbxxx__


#if defined(__AVR_ATmega1281__) || defined(__AVR_ATmega2561__)
// UART
#define RXD         DIO0
#define TXD         DIO1

// SPI
#define SCK         DIO10
#define MISO        DIO12
#define MOSI        DIO11
#define SS          DIO16

// TWI (I2C)
#define SCL         DIO17
#define SDA         DIO18

// timers and PWM
#define OC0A        DIO9
#define OC0B        DIO4
#define OC1A        DIO7
#define OC1B        DIO8
#define OC2A        DIO6
#define OC3A        DIO5
#define OC3B        DIO2
#define OC3C        DIO3


// change for your board
#define DEBUG_LED   DIO46

/**
  pins
 */
#define DIO0_PIN    PINE0
#define DIO0_RPORT  PINE
#define DIO0_WPORT  PORTE
#define DIO0_DDR    DDRE
#define DIO0_PWM    NULL

#define DIO1_PIN    PINE1
#define DIO1_RPORT  PINE
#define DIO1_WPORT  PORTE
#define DIO1_DDR    DDRE
#define DIO1_PWM    NULL

#define DIO2_PIN    PINE4
#define DIO2_RPORT  PINE
#define DIO2_WPORT  PORTE
#define DIO2_DDR    DDRE
#define DIO2_PWM    &OCR3BL

#define DIO3_PIN    PINE5
#define DIO3_RPORT  PINE
#define DIO3_WPORT  PORTE
#define DIO3_DDR    DDRE
#define DIO3_PWM    &OCR3CL

#define DIO4_PIN    PING5
#define DIO4_RPORT  PING
#define DIO4_WPORT  PORTG
#define DIO4_DDR    DDRG
#define DIO4_PWM    &OCR0B

#define DIO5_PIN    PINE3
#define DIO5_RPORT  PINE
#define DIO5_WPORT  PORTE
#define DIO5_DDR    DDRE
#define DIO5_PWM    &OCR3AL

#define DIO6_PIN    PINB4
#define DIO6_RPORT  PINB
#define DIO6_WPORT  PORTB
#define DIO6_DDR    DDRB
#define DIO6_PWM    &OCR2AL

#define DIO7_PIN    PINB5
#define DIO7_RPORT  PINB
#define DIO7_WPORT  PORTB
#define DIO7_DDR    DDRB
#define DIO7_PWM    &OCR1AL

#define DIO8_PIN    PINB6
#define DIO8_RPORT  PINB
#define DIO8_WPORT  PORTB
#define DIO8_DDR    DDRB
#define DIO8_PWM    &OCR1BL

#define DIO9_PIN    PINB7
#define DIO9_RPORT  PINB
#define DIO9_WPORT  PORTB
#define DIO9_DDR    DDRB
#define DIO9_PWM    &OCR0AL

#define DIO10_PIN   PINB1
#define DIO10_RPORT PINB
#define DIO10_WPORT PORTB
#define DIO10_DDR   DDRB
#define DIO10_PWM   NULL

#define DIO11_PIN   PINB2
#define DIO11_RPORT PINB
#define DIO11_WPORT PORTB
#define DIO11_DDR   DDRB
#define DIO11_PWM   NULL

#define DIO12_PIN   PINB3
#define DIO12_RPORT PINB
#define DIO12_WPORT PORTB
#define DIO12_DDR   DDRB
#define DIO12_PWM   NULL

#define DIO13_PIN   PINE2
#define DIO13_RPORT PINE
#define DIO13_WPORT PORTE
#define DIO13_DDR   DDRE
#define DIO13_PWM   NULL

#define DIO14_PIN   PINE6
#define DIO14_RPORT PINE
#define DIO14_WPORT PORTE
#define DIO14_DDR   DDRE
#define DIO14_PWM   NULL

#define DIO15_PIN   PINE7
#define DIO15_RPORT PINE
#define DIO15_WPORT PORTE
#define DIO15_DDR   DDRE
#define DIO15_PWM   NULL

#define DIO16_PIN   PINB0
#define DIO16_RPORT PINB
#define DIO16_WPORT PORTB
#define DIO16_DDR   DDRB
#define DIO16_PWM   NULL

#define DIO17_PIN   PIND0
#define DIO17_RPORT PIND
#define DIO17_WPORT PORTD
#define DIO17_DDR   DDRD
#define DIO17_PWM   NULL

#define DIO18_PIN   PIND1
#define DIO18_RPORT PIND
#define DIO18_WPORT PORTD
#define DIO18_DDR   DDRD
#define DIO18_PWM   NULL

#define DIO19_PIN   PIND2
#define DIO19_RPORT PIND
#define DIO19_WPORT PORTD
#define DIO19_DDR   DDRD
#define DIO19_PWM   NULL

#define DIO20_PIN   PIND3
#define DIO20_RPORT PIND
#define DIO20_WPORT PORTD
#define DIO20_DDR   DDRD
#define DIO20_PWM   NULL

#define DIO21_PIN   PIND4
#define DIO21_RPORT PIND
#define DIO21_WPORT PORTD
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
#define PG5_DDR     DDRG
#define PG5_PWM     &OCR0B


#endif

#ifndef DIO0_PIN
#error "pins for this chip not defined in arduino.h! If you write an appropriate pin definition and have this firmware work on your chip, please submit a pull request"
#endif

#endif /* _FASTIO_ARDUINO_H */
