jonathan-iap/CoilWinder/Arduino/src/Save.cpp

/*
 * Save.cpp
 *
 *  Created on: 5 déc. 2016
 *      Author: jo
 */

#include "Save.h"

Memory::Memory()
: WireSize(0),
  CoilLength(0),
  Turns(0),
  MaxSpeed(0),
  MinSpeed(0),
  AccDelay(0),
  AccIncr(0),

  WinSense(0),
  CarSense(0),

  CarrPass(0),
  CarrStepPerPass(0),
  CarrDir(0),
  CoilTr(0),
  CoilStepPerTr(0),
  CoilDir(0),

  _addr_WireSize(0),
  _addr_CoilLength(0),
  _addr_Turns(0),
  _addr_WinSense(0),
  _addr_CarSense(0),
  _addr_MaxSpeed(0),
  _addr_MinSpeed(0),
  _addr_AccDelay(0),
  _addr_AccIncr(0),
  _addr_DefaultSettings(0),
  _addr_CarrPass(0),
  _addr_CarrStepPerPass(0),
  _addr_CarrDir(0),
  _addr_CoilTr(0),
  _addr_CoilStepPerTr(0),
  _addr_CoilDir(0)
{}




Memory::~Memory(){}



void Memory::init()
{
  // start reading from position memBase (address 0) of the EEPROM. Set maximumSize to EEPROMSizeUno
  // Writes before membase or beyond EEPROMSizeUno will only give errors when _EEPROMEX_DEBUG is set
  EEPROM.setMemPool(MEN_BASE, EEPROMSizeUno);

  _addr_WireSize	    = EEPROM.getAddress(sizeof(char)*BUFFSIZE_WIRE);
  _addr_CoilLength	    = EEPROM.getAddress(sizeof(char)*BUFFSIZE_COIL);
  _addr_Turns		    = EEPROM.getAddress(sizeof(char)*BUFFSIZE_TURNS);
  _addr_MaxSpeed	    = EEPROM.getAddress(sizeof(char)*BUFFSIZE_MAX_SPEED);
  _addr_MinSpeed	    = EEPROM.getAddress(sizeof(char)*BUFFSIZE_MIN_SPEED);
  _addr_AccDelay	    = EEPROM.getAddress(sizeof(char)*BUFFSIZE_ACC_DELAY);
  _addr_AccIncr		    = EEPROM.getAddress(sizeof(char)*BUFFSIZE_ACC_INCR);
  _addr_DefaultSettings	    = EEPROM.getAddress(sizeof(char)*BUFFSIZE_DEFAULT);
  _addr_CarrPass            = EEPROM.getAddress(sizeof(uint16_t));
  _addr_CarrStepPerPass     = EEPROM.getAddress(sizeof(uint16_t));
  _addr_CoilTr              = EEPROM.getAddress(sizeof(uint16_t));
  _addr_CoilStepPerTr       = EEPROM.getAddress(sizeof(uint16_t));
  _addr_WinSense	    = EEPROM.getAddress(1);
  _addr_CarSense	    = EEPROM.getAddress(1);
  _addr_CarrDir 	    = EEPROM.getAddress(1);
  _addr_CoilDir 	    = EEPROM.getAddress(1);
  // If is the first use or if data are corrupted do reset.
  if( !isSet() ) reset();

  // Read and set all data saved in eeprom memory.
  readAll();
}


void Memory::save(char buffer[], const uint8_t id)
{
  //ReadAddresses();
  switch (id)
  {
    case id_WIRESIZE :
      {
	EEPROM.updateBlock<char>(_addr_WireSize, buffer, BUFFSIZE_WIRE);
	break;
      }
    case id_COILLENGTH :
      {
	EEPROM.updateBlock<char>(_addr_CoilLength, buffer, BUFFSIZE_COIL);
	break;
      }
    case id_TURNS :
      {
	EEPROM.updateBlock<char>(_addr_Turns, buffer, BUFFSIZE_TURNS);
	break;
      }
    case id_MAX_SPEED :
      {
	EEPROM.updateBlock<char>(_addr_MaxSpeed, buffer, BUFFSIZE_MAX_SPEED);
	break;
      }
    case id_MIN_SPEED :
      {
	EEPROM.updateBlock<char>(_addr_MinSpeed, buffer, BUFFSIZE_MIN_SPEED);
	break;
      }
    case id_ACC_DELAY :
      {
	EEPROM.updateBlock<char>(_addr_AccDelay, buffer, BUFFSIZE_ACC_DELAY);
	break;
      }
    case id_ACC_INCR :
      {
	EEPROM.updateBlock<char>(_addr_AccIncr, buffer, BUFFSIZE_ACC_INCR);
	break;
      }
    case id_RESUME_SAVE :
      {
	EEPROM.updateInt(_addr_CarrPass, CarrPass);
	EEPROM.updateInt(_addr_CarrStepPerPass, CarrStepPerPass);
	EEPROM.updateInt(_addr_CoilTr, CoilTr);
	EEPROM.updateInt(_addr_CoilStepPerTr, CoilStepPerTr);
	EEPROM.updateBit(_addr_CarrDir, 1, CarrDir);
	EEPROM.updateBit(_addr_CoilDir, 1, CoilDir);
	break;
      }
    case id_W_SENSE :
      {
	EEPROM.updateBit(_addr_WinSense, 1, WinSense);
	break;
      }
    case id_C_SENSE :
      {
	EEPROM.updateBit(_addr_CarSense, 1, CarSense);
	break;
      }
  }
}

void Memory::read(char buffer[], const uint8_t id)
{
  switch (id)
  {
    case id_WIRESIZE :
      {
	EEPROM.readBlock<char>(_addr_WireSize, buffer, BUFFSIZE_WIRE);
	break;
      }
    case id_COILLENGTH :
      {
	EEPROM.readBlock<char>(_addr_CoilLength, buffer, BUFFSIZE_COIL);
	break;
      }
    case id_TURNS :
      {
	EEPROM.readBlock<char>(_addr_Turns, buffer, BUFFSIZE_TURNS);
	break;
      }
    case id_MAX_SPEED :
      {
	EEPROM.readBlock<char>(_addr_MaxSpeed, buffer, BUFFSIZE_MAX_SPEED);
	break;
      }
    case id_MIN_SPEED :
      {
	EEPROM.readBlock<char>(_addr_MinSpeed, buffer, BUFFSIZE_MIN_SPEED);
	break;
      }
    case id_ACC_DELAY :
      {
	EEPROM.readBlock<char>(_addr_AccDelay, buffer, BUFFSIZE_ACC_DELAY);
	break;
      }
    case id_ACC_INCR :
      {
	EEPROM.readBlock<char>(_addr_AccIncr, buffer, BUFFSIZE_ACC_INCR);
	break;
      }
    case id_RESUME_SAVE :
      {
	CarrPass        = EEPROM.readInt(_addr_CarrPass);
	CarrStepPerPass = EEPROM.readInt(_addr_CarrStepPerPass);
	CoilTr          = EEPROM.readInt(_addr_CoilTr);
	CoilStepPerTr   = EEPROM.readInt(_addr_CoilStepPerTr);
	CarrDir         = EEPROM.readBit(_addr_CarrDir, 1);
	CoilDir         = EEPROM.readBit(_addr_CoilDir, 1);
	break;
      }
    case id_W_SENSE :
      {
	WinSense = EEPROM.readBit(_addr_WinSense, 1);
	break;
      }
    case id_C_SENSE :
      {
	CarSense = EEPROM.readBit(_addr_CarSense, 1);
	break;
      }
  }
}

//void Memory::getSavedTotalSteps(uint32_t *totalSteps)
//{
//  *totalSteps = EEPROM.readLong(_addr_TotalSteps);
//}

void Memory::readAll()
{
  // Read the eeprom memory and set buffers with values saved
  read(_buff_WireSize   , id_WIRESIZE);
  read(_buff_CoilLength , id_COILLENGTH);
  read(_buff_Turns      , id_TURNS);
  read(_buff_MaxSpeed   , id_MAX_SPEED);
  read(_buff_MinSpeed   , id_MIN_SPEED);
  read(_buff_AccDelay   , id_ACC_DELAY);
  read(_buff_AccIncr    , id_ACC_INCR);
  read(0                , id_W_SENSE);
  read(0                , id_C_SENSE);


  // Convert value within array in a float or numeric value.
  WireSize 	= atof(_buff_WireSize);
  CoilLength 	= atof(_buff_CoilLength);
  Turns 	= atoi(_buff_Turns);
  MaxSpeed 	= atoi(_buff_MaxSpeed);
  MinSpeed 	= atoi(_buff_MinSpeed);
  AccDelay 	= atoi(_buff_AccDelay);
  AccIncr 	= atoi(_buff_AccIncr);
}

void Memory::reset()
{
  EEPROM.writeBlock<char>(_addr_WireSize, INIT_WIRE, BUFFSIZE_WIRE);
  EEPROM.writeBlock<char>(_addr_CoilLength, INIT_COIL, BUFFSIZE_COIL);
  EEPROM.writeBlock<char>(_addr_Turns, INIT_TURNS, BUFFSIZE_TURNS);
  EEPROM.writeBlock<char>(_addr_MaxSpeed, INIT_MAXSPEED, BUFFSIZE_MAX_SPEED);
  EEPROM.writeBlock<char>(_addr_MinSpeed, INIT_MINSPEED, BUFFSIZE_MIN_SPEED);
  EEPROM.writeBlock<char>(_addr_AccDelay, INIT_ACC_DELAY, BUFFSIZE_ACC_DELAY);
  EEPROM.writeBlock<char>(_addr_AccIncr, INIT_ACC_INCR, BUFFSIZE_ACC_INCR);

  EEPROM.writeBit(_addr_WinSense, 1, WinSense);
  EEPROM.writeBit(_addr_CarSense, 1, CarSense);

  EEPROM.writeBlock<char>(_addr_DefaultSettings, MSG_IS_SET, BUFFSIZE_DEFAULT);

  EEPROM.writeInt(_addr_CarrPass, 0);
  EEPROM.writeInt(_addr_CarrStepPerPass, 0);
  EEPROM.writeBit(_addr_CarrDir, 1, CarrDir);

  EEPROM.writeInt(_addr_CoilTr, 0);
  EEPROM.writeInt(_addr_CoilStepPerTr, 0);
  EEPROM.writeBit(_addr_CoilDir, 1, CoilDir);
}

bool Memory::isSet()
{
  char set[BUFFSIZE_DEFAULT];
  EEPROM.readBlock<char>(_addr_DefaultSettings, set, BUFFSIZE_DEFAULT);

  // True if the two buffers are equals
  return buffercmp((char*)MSG_IS_SET, set, BUFFSIZE_DEFAULT);
}

/* Debug -------------------------------------------------------------------*/
#ifdef DEBUG_
void Memory::ReadAddresses()
{
  Serial.print("adress wire: "); Serial.println(_addr_WireSize);
  Serial.print("adress coil: "); Serial.println(_addr_CoilLength);
  Serial.print("adress turns: "); Serial.println(_addr_Turns);
  Serial.print("adress max: "); Serial.println(_addr_MaxSpeed);
  Serial.print("adress min: "); Serial.println(_addr_MinSpeed);
  Serial.print("adress acc: "); Serial.println(_addr_AccDelay);
  Serial.print("adress win: "); Serial.println(_addr_WinSense);
  Serial.print("adress car: "); Serial.println(_addr_CarSense);
  Serial.print("adress default: "); Serial.println(_addr_DefaultSettings);
  Serial.println(" ");
}

void Memory::ReadFloatValue()
{
  Serial.print("float wire: "); Serial.println(WireSize);
  Serial.print("float coil: "); Serial.println(CoilLength);
  Serial.print("float turns: "); Serial.println(Turns);
  Serial.print("float max: "); Serial.println(MaxSpeed);
  Serial.print("float min: "); Serial.println(MinSpeed);
  Serial.print("float acc: "); Serial.println(AccDelay);
  Serial.print("val win: "); Serial.println(WinSense);
  Serial.print("val car: "); Serial.println(CarSense);
  Serial.println(" ");
}

void Memory::ReadArrayValue()
{
  char _buff_DefaultSettings[BUFFSIZE_DEFAULT] = {0};

  Serial.print("array wire: "); Serial.println(_buff_WireSize);
  Serial.print("array coil: "); Serial.println(_buff_CoilLength);
  Serial.print("array turns: "); Serial.println(_buff_Turns);
  Serial.print("array max: "); Serial.println(_buff_MaxSpeed);
  Serial.print("array min: "); Serial.println(_buff_MinSpeed);
  Serial.print("array acc: "); Serial.println(_buff_AccDelay);
  Serial.print("array win: "); Serial.println(_buff_WinSense);
  Serial.print("array car: "); Serial.println(_buff_CarSense);
  EEPROM.readBlock<char>(_addr_DefaultSettings, _buff_DefaultSettings, BUFFSIZE_DEFAULT);
  Serial.print("array default: "); Serial.println(_buff_DefaultSettings);
  Serial.println(" ");
}
#endif
